BrandonBNguyen/CADMouse/CAD/Encoder KY-040.SLDPRT

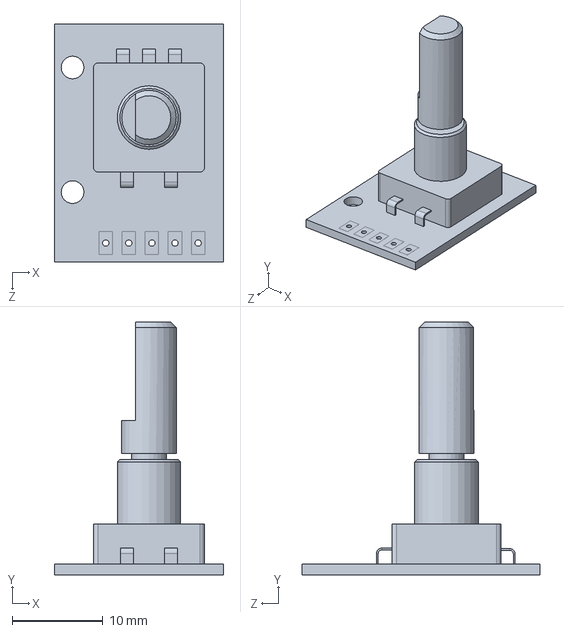
[picture p23: CAD file, 2021-01-27]
CAD/Encoder KY-040.SLDPRT
18.6 x 27.8 x 26.2 mm
