BrandonBNguyen/CADMouse/CAD/KY-040 Encoder/D-handle.SLDPRT

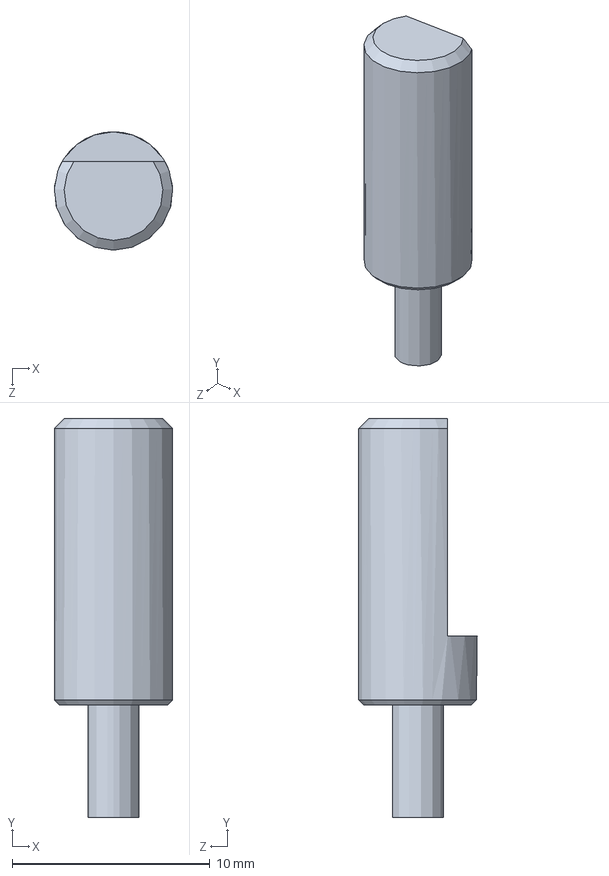
[picture p24: CAD file, 2021-01-27]
CAD/KY-040 Encoder/D-handle.SLDPRT
6.00 x 20.2 x 6.00 mm
