BrandonBNguyen/CADMouse/Test Prints/Rotary Encoder Fix.STL

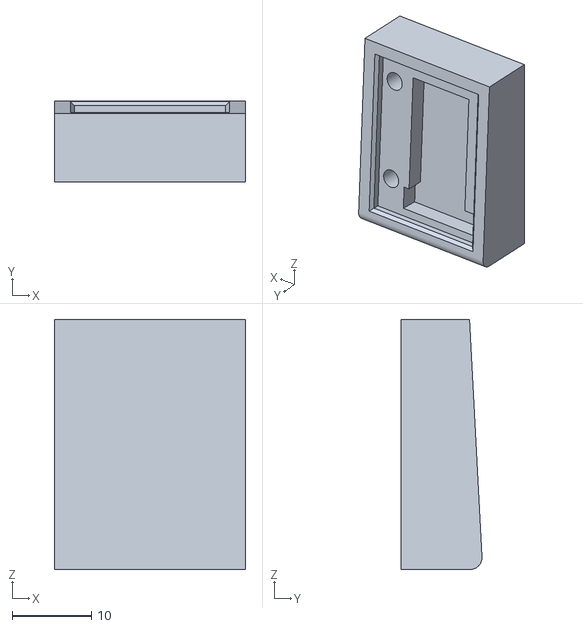
[picture p25: CAD file, 2021-01-27]
Test Prints/Rotary Encoder Fix.STL
24.1 x 10.2 x 31.5
