BrandonBNguyen/CADMouse/CAD/Joystick HW504 Board.SLDPRT

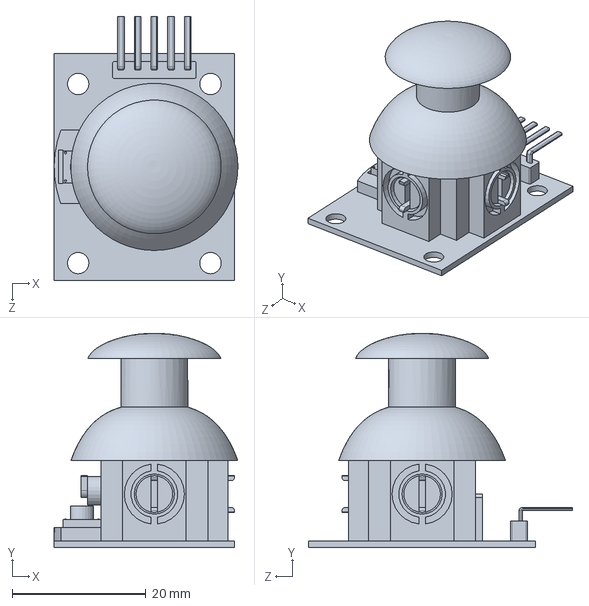
[picture p26: CAD file, 2021-01-27]
CAD/Joystick HW504 Board.SLDPRT
27.5 x 32.0 x 39.5 mm
