BrandonBNguyen/CADMouse/Test Prints/Arduino Micro Holder (Holed).STL

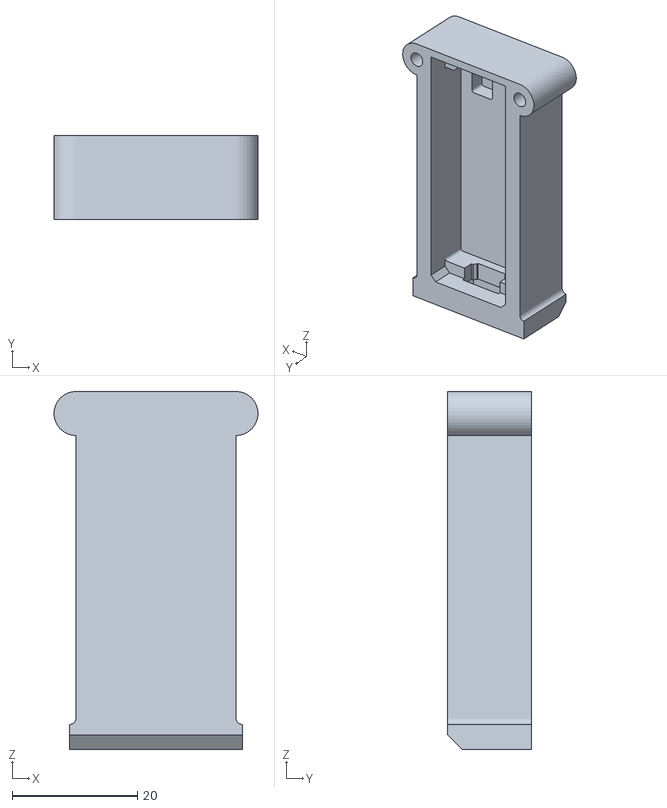
[picture p27: CAD file, 2021-01-27]
Test Prints/Arduino Micro Holder (Holed).STL
32.5 x 13.5 x 57.1
