BrandonBNguyen/CADMouse/Test Prints/Joystick Tester.STL

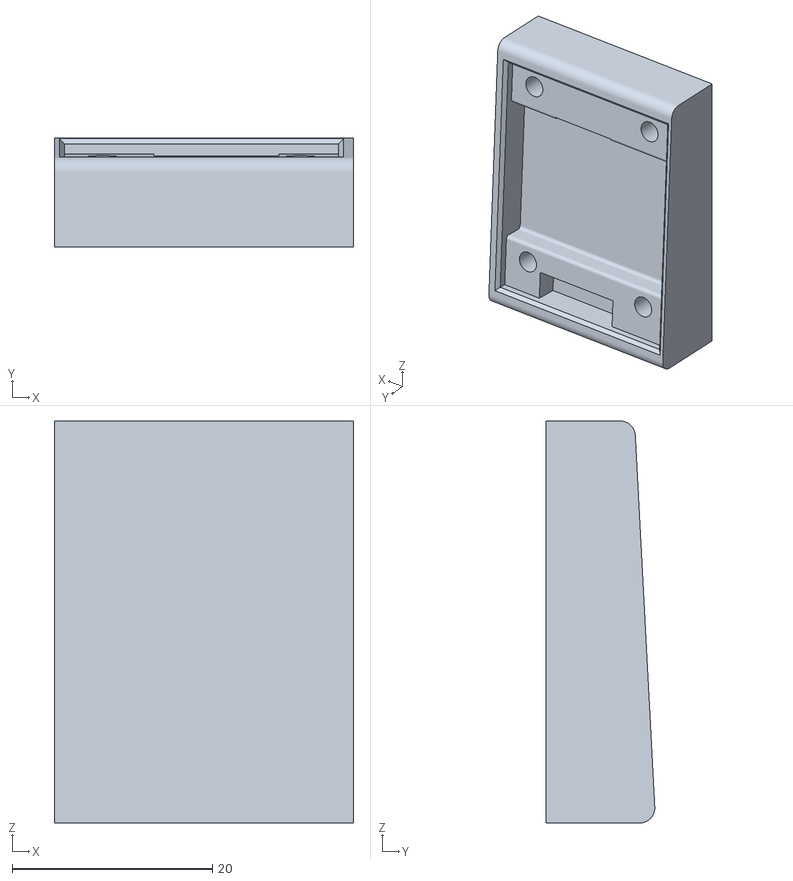
[picture p28: CAD file, 2021-01-27]
Test Prints/Joystick Tester.STL
29.9 x 10.9 x 40.2
