BrandonBNguyen/CADMouse/Test Prints/Rotary Encoder Tester.STL

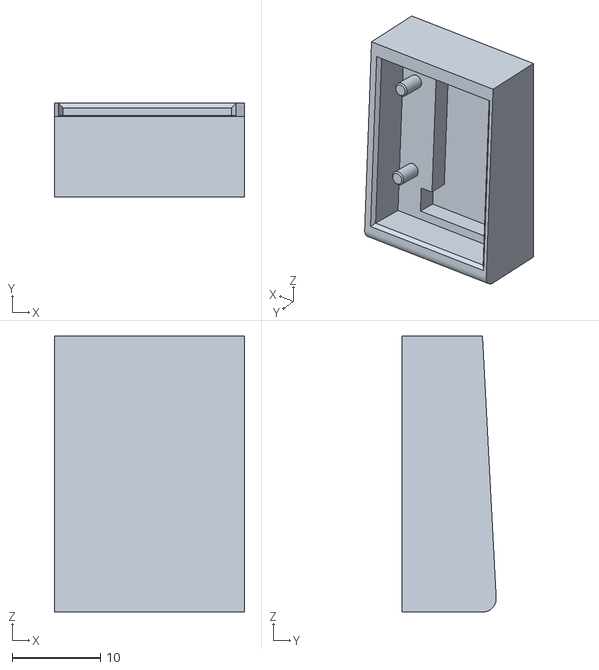
[picture p29: CAD file, 2021-01-27]
Test Prints/Rotary Encoder Tester.STL
21.6 x 10.7 x 31.3
