BrandonBNguyen/CADMouse/Test Prints/Case Bottom Tester.SLDPRT

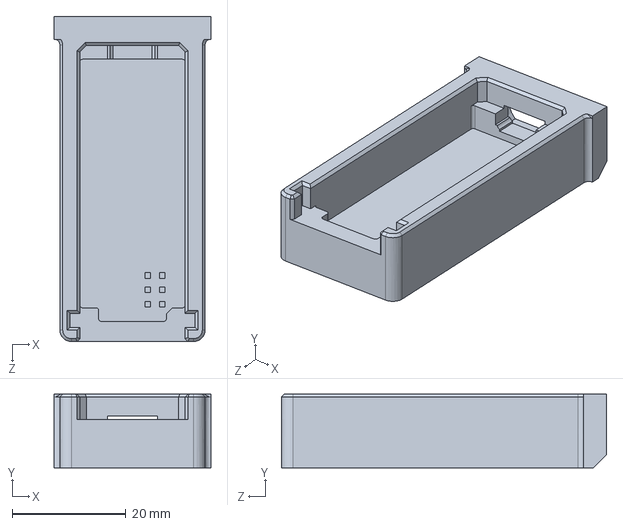
[picture p30: CAD file, 2021-01-27]
Test Prints/Case Bottom Tester.SLDPRT
27.5 x 12.9 x 57.1 mm
